yunusdanabas/evka_position/AGENT_LOG.md

# Agent Activity Log

Historical multi-agent collaboration log. Most recent first.
Format: `date | agent | summary`.

This file is preserved as a historical record; for working rules see
[AGENTS.md](AGENTS.md). Entries below were authored against the guidance files
that existed at the time (notably the git-ignored `CLAUDE.md` and the previous
in-repo `AGENTS.md`). Those historical mentions are intentionally left
unchanged.

## Activity Log

| Date | Agent | Changes |
|---|---|---|
| 2026-08-12 | Claude Code (Opus 5) | **Pre-handoff polish; the 2026-07-29 segfault WIP was wrong and is now actually fixed.** The committed `pytestmark = pytest.mark.forked` approach does not work: it **deadlocks the suite**, deterministically, on Python 3.10 in both a ROS-flavoured conda env and a clean CI-equivalent venv. `tools/calibration/tests/test_gui.py` sorts first and builds a `QApplication` in the parent, so `pytest-forked`'s `os.fork()` from a live-Qt parent inherits locks held by threads that don't exist in the child and blocks forever (killed at 300 s; once at 11 min). It went unnoticed because the recorded green run predates `pytest-forked` being installed — pytest silently ignores an unknown marker, so the markers were inert and the suite was running fully unforked. Replaced with the **two-invocation split** that `REMAINING_WORK.md` had predicted as the fallback: the six modules now carry `pytestmark = pytest.mark.qt_heavy` (registered in `pyproject.toml`), and CI runs `pytest -q -m qt_heavy --forked` then `pytest -q -m "not qt_heavy"` as separate steps — the forked parent never builds a QApplication, and the subtest-bearing modules stay unforked so failures can't be swallowed. Measured in a clean venv (Python 3.10.18, PyQt5 5.15.11, pyqtgraph 0.14.0, numpy 1.26.4, pytest-forked 1.7.5): 44 forked + 160 unforked & 11 subtests = 204; **12 consecutive runs of each pass, 0 failures / 0 segfaults / 0 hangs**; fault injection into a forked module returns `rc=1` and names the test. CI also now installs `pytest-forked` at all (it never did). **Other handoff fixes**: stale `191 tests / 45 checks` corrected to the measured 204/50 in `README.md`, `HANDOFF.md`, and `docs/integration/final_integration_validation.md`; `REMAINING_WORK.md`'s false "seven uncommitted files / last pushed `9553b35`" preamble rewritten (tree is clean, HEAD is current); `numpy` capped `<2` in `requirements.txt` **and** `pyproject.toml` with the Wine/`crealf` reason inline, since that constraint previously lived only in this log; STA defaults (`WIFI_STA_DEFAULT_SSID`/`_PASS` in `firmware/src/SphericalSensor.h`) disclosed in `HANDOFF.md`'s credential section — every doc described the AP credentials and none mentioned the STA ones, in a public repo; dead `.gitignore` rules removed (C# `bin/`/`obj/`/`*.dll`/`*.pdb`/`*.cache`, non-existent `tools/analysis/`, `tools/web_server/`) and `build/`/`dist/` anchored to `/build/`, `/dist/`; `tools/VISUALIZATION_GUIDE.md` deleted (gitignored so it could never clone, unreferenced, and described Three.js/Plotly work never done); v3 DRC JSON + `-backups` debris removed from the v4 PCB workspace and the v3 DRC JSON too, clearing the **last `/home/yunusdanabas` absolute paths from tracked files** (now 0); `matplotlib` requirement noted inline in `laser_radius/report/figures/make_figures.py`. Re-uploaded `EvkaGUI-src-v0.2.1.zip` to the v0.2.1 release so both assets now match local sha256 exactly (the published one had been stamped `02ff485`). Verified: compileall, IPT solver (0.405 mm), 204 pytest, 50 dashboard checks, all 10 PlatformIO envs, fresh-clone link check. No hardware, no flash, no KiCad edits, no history rewrite. |
| 2026-07-31 | Claude Code (Opus 5) | **v0.2.1 released with two GUI zips (one cross-built under Wine)**: tagged `v0.2.1` on `02ff485` and published the GitHub release with two assets. (1) `EvkaGUI-src-v0.2.1.zip` (~172 KB) — new `packaging/evka_gui/build_source_zip.sh`, portable Python source for Linux/macOS operators who previously had no packaged artifact at all; uses `git archive` so only tracked files at HEAD can enter a published zip, and smoke-tests by launching the GUI from a clean extraction. (2) `EvkaGUI-win64-v0.2.1.zip` (79.2 MB) — **cross-built on Linux under Wine 9.0**, not on Windows. Verified as far as that allows: `PE32+ x86-64` binary, `qwindows.dll` bundled, extracted zip ran 40 s in replay mode with no crash log (reference `build_windows.ps1` check is 8 s). **Not verified**: Wine emulates `qwindows.dll` rather than running it natively, and the serial/`COM3` path cannot be exercised under Wine — both stated in the release notes, which ask for a real-Windows check before distribution. **Wine gotcha recorded**: `winetricks vcrun2022` does NOT fix `ucrtbase.dll.crealf` (it installs `ucrtbase.dll` but no `api-ms-win-crt-*` forwarders, so Wine keeps its builtin); the working fix was pinning numpy 1.26.4, since numpy 2.x calls `crealf` on import — meaning this artifact diverges from a real Windows build, which would get numpy 2.x. Prefix lives at the gitignored `/.wine-build/`. Also documented both builders in `packaging/evka_gui/README.md` (`build_source_zip.sh` was previously undocumented) and anchored gitignore rules for both release zips. Found and corrected: the v0.2.0 release asset was stale (built from `04f26e4`, before the export work) — an earlier answer in this session said "no zip needs updating" after checking only the repo and missing GitHub Releases entirely. No hardware, no flash, no KiCad edits. |
| 2026-07-31 | Claude Code (Opus 5) | **Sensor readings in session exports + version 0.2.1**: saved-point and snapshot CSV exports now carry the streamed `wire_mm,theta_deg,phi_deg` triple, appended after the existing columns so position-indexed readers keep working; missing readings are blank cells (blank stays distinguishable from a real `0.0`). `x/y/z` are derived from the spherical triple and EMA-filtered in firmware, so position alone could not be traced back to what the encoders read. Desktop: latched in `_on_sensor` before any software-zero, row types widened in `tools/evka_gui/session_utils.py`, call sites in `tools/evka_gui/gui.py`; the REC session dump was left alone — it is already raw `DATA,` lines whose fields 4/5/6 are exactly this triple, and `parse_line` requires exactly 9 fields. Web dashboard: same columns in `firmware/src/WebDashboard.cpp` (`lastWtp`, cleared on `ws.onclose` so a stale reading cannot attach to a point saved after reconnect). **Latent bugs fixed in the same change**: `gui.py::_refresh_reference_overlays` unpacked saved-point rows as 4-tuples and raised `ValueError` on every 3D repaint once a point was saved (no test covered it; caught by an end-to-end run, regression test added); `tools/calibration/gui.py` shares `write_saved_points_csv` and would have broken on the widened rows, so it latches and exports the triple too. **Duplication removed**: `_export_session` and the dashboard's `endSession` each hand-rolled the CSV/download that `write_saved_points_csv` and `downloadCsv` already provide. Bumped host-tools version `0.2.0`→`0.2.1` in `pyproject.toml`, `build_windows.ps1`, and the tracked docs (historical `AGENT_LOG.md`/`REMAINING_WORK.md` mentions preserved). No Windows zip is checked in — `build_windows.ps1` builds one on Windows from the live `tools/` tree, so no packaging change was needed; validated the spec and import graph with `packaging/evka_gui/build_linux.sh` (frozen app launched and stayed up). Verified: 204 pytest, 50 dashboard checks, compileall, IPT solver (0.405 mm), all 10 PlatformIO envs, `git diff --check`. No hardware, no flash, no KiCad edits. |
| 2026-07-31 | Cursor Agent (Composer) | **README flash commands**: added PlatformIO upload/monitor examples for main device (`esp32s3_v4`, classic `wemos_d1_r32`) and remote control (`button_remote`, optional `button_remote_test`) to [README.md](README.md) and [README_TR.md](README_TR.md). Docs-only; no flash, hardware, or tests. |
| 2026-07-29 | Claude Code (Opus 5) | **Segfault isolation attempt (INCOMPLETE — uncommitted WIP in tree)**: pursued the open CI segfault. Established that blanket `pytest --forked` **fixes** it (0/20 segfaults on Python 3.10 vs 3/20 baseline, ~13 s/run) but is **unsafe**: fault injection proved it silently swallows failing `unittest` subtests — an injected bad assertion in `tools/position_checker/tests/test_math_conventions.py` reported `rc=0, 14 passed` under `--forked` while the same fault correctly reported `rc=1, 7 failed` without it. Blanket forking therefore rejected. Switched to **selective** isolation: added `pytestmark = pytest.mark.forked` to the six pyqtgraph-heavy modules (`test_calibration_report`, `test_command_tracking`, `test_disconnect`, `test_ipt_panel`, `test_recording`, `test_view3d`) so subtest-bearing modules keep normal reporting, plus `pytest-forked>=1.6` in `requirements.txt`. **This selective approach is NOT yet verified** — the 20-run measurement exceeded a 10-minute timeout (forking is much slower) and was stopped before a single clean run was timed. Changes are left uncommitted in the working tree. Remaining steps, evidence, and decision rationale recorded in [REMAINING_WORK.md](REMAINING_WORK.md). Also updated [docs/CI_PYTEST_SEGFAULT_LOG.md](docs/CI_PYTEST_SEGFAULT_LOG.md) with the `--forked` findings. Decisions confirmed by user this session: leave commit `711abf3`'s inaccurate "Playwright" body alone (documented, no history rewrite); god-file splits and missing-module tests approved but **not started**. No hardware, no flash, no KiCad edits, no push. |
| 2026-07-29 | Claude Code (Opus 5) | **Workspace health audit + fixes**: audited the 15-commit rewrite window (`0121b7f`..`33d837b`) — history scope/order/messages clean, no secrets or generated artifacts, `master` synced with `origin/master`. Fixed: `tools/webdash_harness/package.json` hardcoded `python` (failed rc=127 on any host without the alias; CI only passed because `setup-python` provides one) → `python3`; guarded the `PyQt5.QtWebSockets` import in `tools/evka_gui/ws_client.py` so the whole GUI package no longer fails to import on distro PyQt5 (Debian/Ubuntu ship QtWebSockets separately) with `WsClient()` raising a clear error instead, plus `tests/test_ws_import_guard.py`; added `compileall` and IPT-solver steps to `.github/workflows/ci.yml` (both were in AGENTS.md but not CI); removed trailing whitespace in `docs/ASYNCTCP_STACK_OVERFLOW_ANALYSIS.md`; deleted the empty stray `pcb_design/EVKA_position_v3/docs/`. **Found CI red on `master` and did NOT fix it**: `pytest` intermittently segfaults (exit 139) inside pyqtgraph's global `ViewBox.AllViews` walk when building a `PlotWidget` — measured 3/20 failures on Python 3.10, 0/20 on 3.12. Four candidate fixes were implemented, measured, and reverted as ineffective or harmful; full investigation, traceback, failure-rate table, and recommended next step (process isolation via `pytest-forked`) recorded in [docs/CI_PYTEST_SEGFAULT_LOG.md](docs/CI_PYTEST_SEGFAULT_LOG.md). Also noted: commit `711abf3`'s body says "Playwright" but the harness is jsdom (not amended — history already pushed); `v0.2.0-prototype` tag sits on `backup/pre-split-20260729`, not on `master`. Verified: 193 pytest, 45 dashboard checks, compileall, IPT solver (0.405 mm), and all 5 PlatformIO envs. No hardware, no flash, no KiCad edits, no history rewrite. |
| 2026-07-29 | OpenCode (GLM-5.2) | **Agent guidance consolidation (4 commits)**: (1) created tracked `AGENT_LOG.md` preserving the full historical activity table; (2) rewrote `AGENTS.md` as a concise universal agent guide and removed the `AGENTS.md`/`CLAUDE.md`/`CODEX.md`/`COPILOT.md` exclusions from `.gitignore` so guidance changes transfer on clone; (3) replaced retired `CLAUDE.md` and old activity-log references across `docs/ASYNCTCP_STACK_OVERFLOW_ANALYSIS.md`, `docs/resources.md`, `docs/hardware_design/12v_legacy/README.md`, `docs/hardware_design/12v_legacy/12v/circuit_schematic_12v.md`, `laser_radius/RESEARCH_PROMPT.md`, `laser_radius/kinematics_and_calibration.md`, `laser_radius/firmware_integration.md`; (4) indexed `AGENTS.md` and `AGENT_LOG.md` in `HANDOFF.md` and `docs/README.md`, and added this entry. Moved the local unpushed `v0.2.0-prototype` tag to the final commit. No pushes, tests, hardware checks, or remote changes. |
| 2026-07-29 | OpenCode (GPT-5.6) | **Agent guidance consolidation**: split the multi-purpose `AGENTS.md` into a concise tracked [AGENTS.md](AGENTS.md) working guide and this tracked `AGENT_LOG.md` history store; deleted the redundant git-ignored `CLAUDE.md`; removed the `AGENTS.md`/`CLAUDE.md`/`CODEX.md`/`COPILOT.md` exclusions from `.gitignore` so guidance changes cannot remain silently local; updated active `CLAUDE.md` and old activity-log references in `HANDOFF.md`, `docs/README.md`, `docs/resources.md`, `laser_radius/RESEARCH_PROMPT.md`, `laser_radius/kinematics_and_calibration.md`, `laser_radius/firmware_integration.md`, `docs/ASYNCTCP_STACK_OVERFLOW_ANALYSIS.md`, `docs/hardware_design/12v_legacy/README.md`, and `docs/hardware_design/12v_legacy/12v/circuit_schematic_12v.md`; preserved historical mentions inside this log. Moved the local unpushed `v0.2.0-prototype` tag to the final commit. No pushes, tests, hardware checks, or remote changes. |
| 2026-07-29 | OpenCode (GPT-5.6) | **Prototype handoff implementation and software freeze**: completed unified GUI/dashboard/calibration correctness work; added strict response tracking, STATUS parsing, timeout recovery, zero-relative RAW diagnostics, ACK-confirmed PPR flows, report overlap/stale-artifact guards, transactional session writes, and candidate-transform safety. Removed vendor C# sources, rejected shared calibration JSON, evka_gui_v2 shims, and tracked LaTeX intermediates. Set host tools 0.2.0 / Python 3.10+, pinned the jsdom dashboard harness, expanded CI, finalized self-contained English/Turkish handoff/protocol/calibration docs, and retained hardware validation as explicitly deferred. Software-only verification: 191 pytest, 45 dashboard checks, compileall, IPT solver (0.405 mm), and all 10 PlatformIO environments passed; no flash, hardware check, push, or remote change. |
| 2026-07-29 | OpenCode (GPT-5.6) | **Post-cleanup documentation reconciliation**: updated active handoff, onboarding, protocol, calibration, integration, v4, and host-tool docs for completed vendor C# deletion, host tools `0.2.0` / Python 3.10+, pending software-verification result slots, and no checked-in shared/default calibration JSON. Canonical `tools/evka_gui` remains sensor-frame-only; a passing session JSON is documented only as an explicit `--legacy-visualizer --calibration PATH` input. Preserved archived C# history as clearly deleted. Docs-only; no builds, tests, uploads, or hardware checks. Verified `git diff --check` and 130 active relative Markdown links across 29 files. |
| 2026-07-29 | OpenCode (GPT-5.6) | **Approved prototype firmware/dashboard correctness**: retained zero-relative `RAW_COUNTS`; centralized one-response command dispatch so serial/TCP/WebSocket errors are consistent; made `CAL_W` use count magnitude with strict finite/range validation; made classic/v4 encoder signs board-specific without changing pins; added WPA2 63-character password limit and verified NVS ACKs; made dashboard rotary PPR sharing explicit and apply/save status ACK+CONSTANTS-driven; rejected overlong/full WebSocket commands instead of truncating/dropping silently. Verified embedded JS syntax plus `pio run -e wemos_d1_r32` and `pio run -e esp32s3_v4`. |
| 2026-07-16 | OpenCode (GPT-5.5) | **Calibration report CLI**: added `python -m tools.calibration.report` default workflow. First run creates `docs/calibration/sessions/current/calibration_points.csv` and `validation_points.csv`; subsequent runs generate `report.md`, `calibration.json`, `calibration_errors.csv`, and `validation_errors.csv` from the filled CSVs using the existing Kabsch solver. Added focused tests under `tools/calibration/tests/` and documented the command in `tools/calibration/README.md`. |
| 2026-07-14 | OpenCode (GPT-5.5) | **ButtonRemoteTest pin-scan command + flash**: added TCP/USB serial commands to `firmware/tests/ButtonRemoteTest/ButtonRemoteTest.cpp` (`PING`, `PINS`, `HELP`), with `PINS` reporting GPIO `0,1,2,3,4,5,6,7,8,9,10,20,21` while excluding flash pins `11–17` and USB `18/19`. Added **READ PINS** button/display to `tools/remote_tester/remote_test_gui.py`. Built and flashed `button_remote_test` to `/dev/ttyACM0`; serial sanity check returned `PINS,GPIO0=1,...,GPIO21=1` and AP `REMOTE_TEST` came up at `192.168.4.1`. Verify: `pio run -e button_remote_test`; `pio run -e button_remote_test --target upload --upload-port /dev/ttyACM0`; USB serial `PINS`; `python -m compileall tools/remote_tester tools/evka_gui -q`. |
| 2026-07-14 | OpenCode (GPT-5.5) | **evka_gui no-dock/no-scroll layout pass**: moved protocol log from bottom dock into a compact left-column panel, removed the left `QScrollArea`, moved IPT / Points / Diagnostics into tabs, moved Battery and ESP-NOW remote into Diagnostics, and moved right-column controls above the plot grid so the bottom/right area remains plots. Compact connection panel now permits 50/50 split at 1366×768 and 1920×1080. Verify: `pytest tools/evka_gui/tests -q` 34 passed; `python -m compileall tools/evka_gui -q`; offscreen 1920×1080 split `[957, 957]`, 1366×768 split `[680, 680]`; no `QDockWidget`, left panel is `QWidget`. |
| 2026-07-14 | OpenCode (GPT-5.5) | **evka_gui full-page polish + bug pass**: restored true 50/50 maximized splitter behavior with horizontally expanding control panel, enlarged/stretch-based saved-points list, compact 160px protocol-log dock, and 2D origin/saved-point layer markers. Fixed protocol log UI-thread updates, TCP XYZ log classification, WebSocket connect timeout/state cleanup, malformed `POINT` parsing, rejected IPT solution action gating, and Remote Tester TCP thread cleanup. Added focused tests for protocol classification, WebSocket URL parsing, control-line ingestion, saved-points CSV, and profiles. Docs updated for inline Quick IPT + WebSocket examples. Verify: `pytest tools/evka_gui/tests -q` 34 passed; `python -m compileall tools/evka_gui -q`; offscreen `EvkaWindow`/`RemoteTesterWindow` smoke OK; offscreen 1920×1080 split `[957, 957]`, 1366×768 split `[680, 680]`. |
| 2026-07-14 | Cursor Agent | **evka_gui layout de-clutter**: left control column capped at 540px with view-first splitter (480/1120 default, stretch 0:1); Commands / Points / Diagnostics moved into tab widget (SYSINFO + PPR + raw counts in Diagnostics); quick commands in 3-column grid; saved-points list max height 140px; view grid row/column stretch for larger 3D/2D plots; Quick IPT spacing tightened (`ipt_panel.py`). Protocol log dock + replay bar (replay-only) unchanged. Tests: 27 passed; offscreen `EvkaWindow` OK. |
| 2026-07-14 | Cursor Agent | **Remote tester layout fix**: `_header_widget()` hook in `remote_test_gui.py` with log stretch; `remote_window.py` dev note via hook instead of `insertWidget(0)` (was clipping fixed 580px layout); min 480×560, default 520×680. |
| 2026-07-14 | Cursor Agent | **EVKA GUI full enhancement (Phases 1–6)** — session: snapshot capture/clear/export CSV (`session_utils.py`), saved-points CSV export, saved-point label refresh on SW zero (`UserRole` + `_refresh_saved_point_labels`), connection profiles (save/load/delete via `QSettings`). UI polish: plot layer toggles (trail/IPT/origin/saved), trail max spinbox, keyboard shortcuts (`Z`/`S`/`A`/`Esc`), copy axis/Rθφ buttons, threshold alerts (invalid position, low battery, low heap). Transport/diagnostics: WebSocket mode (`ws_client.py`, QWebSocket port 80 `/ws`, `--ws HOST` CLI), protocol log dock (`protocol_log.py`), Open Dashboard toolbar, CONSTANTS/PPR strip, `RAW_COUNTS` firmware command → `RAW,<θ>,<φ>,<wire>` in `EvkaPosition.cpp` + `model.py` parsing. IPT depth: Copy P / export capture CSV / Add P to snapshots in `ipt_panel.py`, 3D IPT overlay on `_View3D` (`position_checker/gui.py`), sweep hints from `solver.py` constants. Replay: pause/speed/step/slider seek with replay-from-zero rebuild (`replay_utils.py`). Calibration: Kabsch write `calibration.json` + endpoint CSV import in `calibration.py`. Remote: **Remote Tester…** secondary window (`remote_window.py`, wraps `tools/remote_tester`). Key files: `gui.py`, `session_utils.py`, `protocol_log.py`, `ws_client.py`, `replay_utils.py`, `remote_window.py`, `ipt_panel.py`, `wifi_window.py`, `ipt_window.py`, tests `test_session_utils.py`, `test_replay_utils.py`, `test_ipt_panel.py`, `test_ipt_window.py`, `test_model.py`. Docs: `tools/evka_gui/README.md`, `docs/gui_unification/LOG.md`, `PLAN.md`, `CMD_SOFTWARE_INTEGRATION.md`, `README.md` (RAW_COUNTS), `remote_tester/README.md`. Verify: `pytest tools/evka_gui/tests -q` 27 passed, `pio run -e esp32s3_v4` OK, offscreen `EvkaWindow` OK. Deferred: laser radius GUI (no firmware); live `calibration.json` transform in GUI. |
| 2026-07-14 | Cursor Agent | **Inline IPT + WiFi window** (plan: inline IPT on main page): created `tools/evka_gui/ipt_panel.py` — inline **Quick IPT** group (L, ARM/STOP/SOLVE/CLEAR, P/L_hat/RMS/cond/status) on main scroll panel; green cloud + orange target + dashed sphere overlays on session XY/XZ/YZ plots via `_refresh_ipt_overlays()` in `gui.py`; always feed raw lines in `_drain` (sensor frame, not SW-zero offsets). Created `tools/evka_gui/wifi_window.py` — **WiFi Settings…** secondary window (SSID/password, Save & Reboot, Forget, router IP); removed WiFi credential fields from main panel. Compact SYSINFO one-liner strip (RSSI · heap · uptime · TCP). Refactored `ipt_window.py` → `IptPlotsWindow` (plots-only pop-out sharing `IptPanel` state); toolbar **IPT plots…**. Tests: `test_ipt_panel.py`. Doc sweep: `docs/gui_unification/PLAN.md`, `tools/evka_gui/README.md`, `tools/README.md`, `CMD_SOFTWARE_INTEGRATION.md`, `HANDOFF.md`, `CONTRIBUTING.md`. |
| 2026-07-14 | Cursor Agent | **Quick IPT in evka_gui**: toolbar **Quick IPT…** secondary window (`tools/evka_gui/ipt_window.py`) fed from main `_drain` with raw protocol lines; reuses `tools/ipt` capture/solver; standalone `python -m tools.ipt` unchanged. Tests: `tools/evka_gui/tests/test_ipt_window.py`. Doc sweep: README, tools/README, HANDOFF, CONTRIBUTING, PLAN, CMD integration, v4 FIRMWARE, ipt README. |
| 2026-07-13 | OpenCode (GPT-5.5) | **Python EVKA GUI 3D view rotation**: changed only the unified Python GUI initial 3D camera by parameterizing `_View3D` defaults and instantiating `tools.evka_gui` with `rot_x=30.0`; left coordinate math, data signs, browser dashboard, and legacy standalone visualizer default unchanged. |
| 2026-07-13 | OpenCode (GPT-5.5) | **v4 encoder sign correction**: flipped `ENCODER_THETA_SIGN` to `+1.0f` and `ENCODER_PHI_SIGN` to `-1.0f` after field check showed upward motion produced negative phi/Z and desired +Y produced negative theta/Y. Updated `CLAUDE.md`, `docs/ARCHITECTURE.md`, and `docs/calibration/README.md`; no pin-map changes. Verified `pio run -e esp32s3_v4`. |
| 2026-07-13 | OpenCode (GPT-5.5) | **v4 THETA/WIRE port swap**: backed up `pcb_design/EVKA_position_v4/` to `/tmp/opencode/EVKA_position_v4_backup_20260713_141439/`; updated v4 KiCad schematic, PCB, and BOM CSV so J1 is WIRE and J3 is THETA while leaving PHI on J2; updated `SphericalSensor.h` v4 pins to THETA GPIO9/10 and WIRE GPIO7/8; updated current v4 docs/calibration notes with connector order and encoder cable color codes; copied missing TP4056, MT3608, and ESP32-S3 symbol/footprint assets into the repo-local v4 `libs/` and added project `sym-lib-table`. |
| 2026-07-09 | OpenCode (Qwen) | **Bosch PLR 40 C integration research — RESOLVED** (docs-only, no firmware/PCB changes): Bluetooth type discrepancy resolved — Bosch's official PLR 30 C / PLR 40 C manual explicitly states **"Bluetooth 4.2 (Low Energy)"** and **"must support the GATT profile."** ESP32-S3 compatibility confirmed (BLE-only chip matches BLE-only device). Protocol decrypted from GLM family: BLE UUIDs (`02a6c0d0-...` service, `02a6c0d1-...` characteristic), CRC-8 (polynomial 0xA6, init 0xAA), IEEE 754 float parsing (bytes 7-10, little-endian), command table (continuous sync `C0 55 02 01 00 1A`, single measure `C0 40 00 EE`). **However:** byte-level traces are from GLM 50C/50CG/120C — not yet verified on physical PLR 40 C. One real-device capture session required before firmware work. USB interface: none (no USB port on PLR 40 C). **Recommendation updated:** do not use PLR 40 C for production — BLE latency jitter, no wired fallback, 5-minute auto-power-off, power supply fragility make it unsuitable for continuous automated tracking. Use wired industrial sensors (Meskernel LDK-40/LDL-T or Dimetix D-Series) instead. Updated `laser_radius/bosch_plr_40c_integration.md` with full confirmed details, NimBLE code sketches, risk assessment. Updated `laser_radius/version_a_handheld_devices.md` §2.3 to mark Bluetooth type as confirmed. Updated `laser_radius/firmware_integration.md` §2 with confirmed BLE details, UUIDs, CRC-8 code, IEEE 754 parsing. Updated `laser_radius/README.md` executive summary and folder index. Deleted `laser_radius/BOSCH_PLR_40C_DEEP_RESEARCH_PROMPT.md` (research complete). |
| 2026-07-09 | OpenCode (Qwen) | **Bosch PLR 40 C integration research** (docs-only, no firmware/PCB changes): discovered critical Bluetooth type discrepancy — prior docs stated "BLE 4.2 only (GATT)" but the only community reference implementation ([philipptrenz/BOSCH-GLM-rangefinder](https://github.com/philipptrenz/BOSCH-GLM-rangefinder), archived 2024-07-03) uses **classic Bluetooth RFCOMM (SPP)**, not BLE. Created `laser_radius/bosch_plr_40c_integration.md` with full analysis: reverse-engineered protocol details (measure command `\xC0\x40\x00\xEE`, response parsing `uint32(data[2:6]) * 0.05` mm), ESP32-S3 integration sketches for both SPP and BLE paths, verification steps (nRF Connect scan to determine Bluetooth type), and risk assessment. Created `laser_radius/BOSCH_PLR_40C_DEEP_RESEARCH_PROMPT.md` with comprehensive research prompt for further investigation (Bluetooth type verification, protocol confirmation, USB interface investigation, ESP32-S3 specific integration, comparison with alternatives). Updated `laser_radius/version_a_handheld_devices.md` §2.3 to flag both measurement principle AND Bluetooth type as unconfirmed (two independent flags). Updated `laser_radius/firmware_integration.md` to add §2 (Bosch PLR 40 C protocol details) and corrected interface table to note Bluetooth type is unconfirmed. Updated `laser_radius/README.md` folder index with new files. |
| 2026-07-09 | OpenCode (GPT-5.5) | **GUI consolidation and battery protocol parity**: created the tracked unification plan/log under `docs/gui_unification/`, established `tools/evka_gui` as the canonical Python operator GUI with `python -m tools.evka_gui` / `evka-gui`, added deprecated `tools/evka_gui_v2` compatibility shims, and updated docs to point users at the unified GUI. Added missing operator features in the canonical GUI (TCP/WebSocket connect paths, replay-safe controls, min/max/origin-distance display/export, per-axis zero, calibration capture helpers) while leaving `tools/ipt/` and `tools/remote_tester/` untouched. Added TCP/WebSocket `BATT,<voltage>,<pct>,<is_low>` parity after `STATUS`, WebDashboard battery polling/display, and Windows CMD `BATT` parsing. Verified `pytest tools/evka_gui/tests -q`, `python -m compileall tools/evka_gui tools/evka_gui_v2 tools/position_checker`, offscreen Qt `EvkaWindow` instantiate, `pytest -q` (62 passed), `pio run -e esp32s3_v4`, and `dotnet build CMDScanner.csproj` (success with existing nullability warnings). |
| 2026-07-01 | Claude Code | **Laser radius study — extended hardware research + report restore** (docs-only, no firmware/PCB changes): restored the accuracy-vs-range chart (Figure 1) to `laser_radius/report/report.tex` after it was removed in a prior pass. Ran two parallel Copilot CLI research agents (per user request) to broaden the device shortlist: Version A gained 8 candidates (Hilti PD-I, Leica DISTO D2/S910, Bosch GLM 50-27CG/165-27CG, Stanley TLM165i, RS PRO/CEM iLDM-150H — cheapest BLE handheld found at ~$90-130 — and ADA Cosmo 60 Green), plus 5 more rejected devices documented (DeWalt DW099S too-short-range, Makita LD050P no interface, Skil ME981901, Trimble/Spectra Precision QM-series no interface, Nikon Forestry Pro II wrong tech). Version B gained 5 industrial candidates (Micro-Epsilon optoNCDT ILR1181-3/ILR2250/ILR3800, WayCon LDI, Jenoptik LDM4x, Scantron SLS) plus a documented 13-manufacturer rejection list (SICK/Banner/Wenglor/Balluff/Contrinex/Riftek/di-soric/Acuity/Pepperl+Fuchs/Baumer confirmed wrong tech; ifm O1D inconclusive; Jenoptik LDM7x/LDM301-302 same-family-different-tech trap) and one flagged near-miss (Leuze ODSL 30 — genuinely phase-based but %-accuracy, fails spec anyway). Total qualifying shortlist grew from 5 to 17 devices. Updated all 5 `laser_radius/*.md` files + `README.md` with the expanded tables and standout picks (Leica DISTO S910 = best overall spec with native USB; RS PRO ILDM-150H = potential Bosch price replacement). Regenerated `report/figures/accuracy_vs_range.png` with 5 representative lines (two "meets spec" flat-accuracy bands, JRT's slight-growth line, and two "fails spec" examples for different reasons — wrong tech vs. right-tech-wrong-accuracy-type). Added a curated "Extended Shortlist" table + updated recommendations to `report/report.tex`, fixed a table-column overflow, recompiled clean (6 pages). |
| 2026-07-01 | Claude Code | **Laser radius study re-scoped to a fixed spec + LaTeX report** (docs-only, no firmware/PCB changes; supersedes the tiered version below from earlier the same day): user fixed the actual requirement — range ≤40 m, laser device accuracy ≤10 mm (device spec, not combined-system XYZ, confirmed with user) — replacing the earlier 3-tier framework. Rewrote all 5 `laser_radius/*.md` files + `README.md`: the physics dividing line is phase-shift (AMCW) vs. pulsed-ToF measurement — the entire Benewake TF-series (previously the Version B primary pick) fails the new spec (±5cm–±1%, 5–40× over budget) and is now excluded with the physics reason documented; new shortlist is JRT B605B (≈±2.6mm@40m, RS232 TTL, primary low-cost pick, works as Version A or B), Meskernel LDL-T (±1mm/80m, 30Hz), Bosch PLR 40C (±2mm confirmed flat across full 0.05–40m range, BLE fallback, best Turkey stock), Leica DISTO X4/D-series (±1mm, premium, genuine RS232 accessory cable), Dimetix D-series (±1mm, RS232/RS422, confirmed CHF 1,769–2,437 on manufacturer's own shop — primary Version B industrial pick). Noted the Version A/B convergence at this accuracy bar (bare OEM modules work either mounted style). `kinematics_and_calibration.md` §4 reframed the combined-error-budget finding (encoders alone contribute ≈17.8mm at 40m regardless of laser choice) as informational context, not a redesign trigger, per the user's explicit scope decision. Added **`laser_radius/report/`**: a 6-page LaTeX report (`report.tex`/`report.pdf`, compiles clean with `pdflatex`) summarizing the study, with 2 generated matplotlib figures (`figures/accuracy_vs_range.png`, `figures/error_budget.png`), a TikZ kinematic-chain diagram, and TikZ placeholder boxes (not `\includegraphics`) for hardware photos the user will add later under `report/images/`. |
| 2026-07-01 | Claude Code | **Laser radius detailed study** (docs-only, no firmware/PCB changes) — superseded same day by the entry above: expanded the brief into 5 new files under `laser_radius/` — `version_a_handheld_devices.md` (5 wired-serial/BLE candidates incl. JRT B605B, Meskernel LDL, Dimetix DLS-B, Bosch PLR 40 C BLE fallback; explains why UNI-T LM50A has no automated data path), `version_b_integrated_modules.md` (TF02-i-RS485 primary + 5 alternatives, Modbus wiring), `kinematics_and_calibration.md` (laser offset geometry, `CAL_R`/`ZERO_R` workflow proposal replacing `CAL_W`, combined error-budget table showing encoder angular error dominates at 40m regardless of laser choice), `firmware_integration.md` (interface options, 20Hz feasibility, BLE+WiFi coexistence notes, `LaserRadiusSensor` API sketch — design only, not implemented), `procurement_and_bom.md` (pricing/suppliers, bench-test order). Key finding: the brief's RS-485 GPIO 13/14/18 baseline came from the archived `12v_legacy/v2` pin plan; the current as-built 5V v2 board wires those pins differently (13/14=AUX header, 18=BTN2) — documented corrected wiring (13/14/15) as an open item for PCB-owner review, no `.kicad_sch` touched. Updated `laser_radius/README.md` with an executive summary, 3 proposed requirement tiers, and an A-vs-B recommendation; updated folder index. Research sourced via live web search (device specs/pricing/Turkey availability), with unverified figures explicitly flagged "verify before order" throughout. |
| 2026-07-01 | Cursor Agent | **Laser radius research at repo root**: Moved brief to `laser_radius/README.md`; added `laser_radius/RESEARCH_PROMPT.md` for Claude deep-dive; left redirect stub at `docs/research/laser_radius_research.md`. Detailed files (Version A/B, kinematics, firmware, BOM) to be added under `laser_radius/`. |
| 2026-07-01 | Cursor Agent | **Laser radius research brief**: Added `docs/research/laser_radius_research.md` — preliminary doc for spherical variant with 2 rotary encoders + laser (not draw-wire). Covers Version A (detachable handheld; wired serial preferred, Bosch PLR BLE fallback; LM50A noted unsuitable) and Version B (built-in Benewake TF02-i-RS485). ESP32-S3 phi-head mounting, kinematic chain, pin baseline, open questions for full research phase. Docs-only; no firmware changes. |
| 2026-06-24 | Cursor Agent | **Encoder sign constants for +Z up / +X forward**: Added `ENCODER_THETA_SIGN` (-1.0) and `ENCODER_PHI_SIGN` (+1.0) in `SphericalSensor.h`; applied in `countsToSpherical()` (replaces hardcoded phi negation). Updated `CLAUDE.md`, `AGENTS.md`, `system_architecture.md`, `docs/calibration/README.md`. Verified `pio run -e wemos_d1_r32` + pytest (42 tests). |
| 2026-06-24 | Cursor Agent | **CMD GUI Software Zero fix + audit**: Added `tools/position_checker/cmd_display.py` with testable offset/refresh logic. Fixed immediate R/θ/φ refresh on Software Zero click; added Clear Software Zero button, SW ZERO badge, invalid-position XYZ styling, SYSINFO TCP count, open-network WiFi, disconnect state reset, saved-point display/world labels + ERR:NO_POINTS dialog, legacy BAGLI_DEGIL STA_IP. Updated `cmd_gui.py`, `parser.py` (isfinite on XYZ/SENSOR), C# `gui.cs` parity (immediate refresh + ACK-wait WiFi). Added `test_cmd_gui_zero.py`, `test_tcp_client.py`. Updated `tools/README.md` and `docs/integration/CMD_SOFTWARE_INTEGRATION.md`. 42 tests pass. |
| 2026-06-24 | OpenCode (Qwen) | **IPT feature implementation**: Created `tools/ipt/` package with Quick IPT hidden-point measurement (sphere-fit solver, armed capture buffer, PyQt5 GUI). Added finite-value guard to TCP ingest, clarified known-L semantics (L_fit for sanity check), expanded README with workflow/troubleshooting/limitations. Created LaTeX technical report under `docs/reports/ipt/`. Added IPT to `tools/README.md` and root `README.md`. Fixed network doc inconsistencies: aligned `README.md`, `CLAUDE.md`, and `docs/integration/CMD_SOFTWARE_INTEGRATION.md` with firmware source of truth (`SphericalSensor.h`: STA IP `192.168.1.84`, GW `192.168.1.254`, SSID `ASMETAL`). All 39 tests pass. |
| 2026-04-29 | OpenCode (kimi-k2.6) | **Archived all 12V hardware designs** into `docs/hardware_design/12v_legacy/` after project direction changed away from 12V. Moved folders: `12v`, `12v_tht`, `v2`, `v3`, `final_design`, `comparison`. Updated all internal and external cross-references in `AGENTS.md`, `CLAUDE.md`, `firmware/src/SphericalSensor.h`, and files inside `12v_legacy` (including KiCad schematic text fields and presentation HTML). Added `12v_legacy/README.md` as archive index. |
| 2026-04-29 | OpenCode (GPT-5.5) | Expanded onboard-charging comparison guidance in `docs/hardware_design/12v_legacy/comparison/`: added V3-D charger module choices (12.6V 1A/2A/4A, Type-C 2A, IP2369/IP2326 PD branches), BMS pairing table (6A/20A/25A/40A/60A plus Daly/JBD preference), charge-only vs power-path/load-sharing architecture ranking, and Options A/B/C for future onboard charging. Updated the 18-slide comparison deck and `final_design/README.md` future-revision guidance while keeping Final Design as external-balance-charge-only. |
| 2026-04-29 | OpenCode (GPT-5.5) | Reworked `docs/hardware_design/12v_legacy/comparison/` deliverables in English: rewrote `HARDWARE_COMPARISON.md` as the primary Final Design decision guide, rebuilt `presentation/index.html` as an 18-slide Reveal.js companion, and updated `README.md` to recommend Final Design consistently. Corrected TP5100 3S charging claims based on source review plus external fact check, clarified Schottky OR priority ambiguity, added 1S/2S/3S LiPo charging-method comparisons, added optional `V3-D Onboard 3S Charger Module` branch with verified charger+BMS/load-isolation requirements, updated `final_design/README.md` future onboard-charging guidance, and downgraded Final Design wording from validated to reviewed/selected pending ESP32-S3 firmware migration and physical validation. |
| 2026-04-27 | OpenCode (GPT-5.5) | Created `docs/hardware_design/12v_legacy/final_design/` as the final recommended build package copied from the V3-A direction and extended into a single 12V-only external-charge design. Added README, source-copy manifest, final schematic, BOM, LPKF layout guide, pin assignment, external charging procedure, validation checklist, and `firmware/pin_assignment_final.h`. Final design adds `D_ADAPT` adapter isolation to prevent battery backfeed into the adapter-sense/Q_BATT gate rail and omits onboard charging/V3-B/V3-C options. |
| 2026-04-27 | OpenCode (GPT-5.5) | Created `docs/hardware_design/12v_legacy/comparison/README.md`, an independent comparison of the legacy 5V board, original 12V design, 12V all-THT variant, V2 industrial ESP32-S3 design, and V3-A/B/C simple ESP32-S3 variants. Covered individual pros/cons, safety, manufacturing, firmware readiness, use-case fit, and final recommendation of V3-A for new core 12V builds. |
| 2026-04-27 | Claude Code | **V3 hardware documentation review** (code-review pass, docs-only fixes). Found 3 issues: (F1) ADC tap inconsistency — block diagram showed `V12_PROT`, section 6 said `BUCK_VIN`; fixed block diagram in `circuit_schematic_v3.md` and removed hedge in `pin_assignment_v3.md` line 12. (F2) `BMS_3S` qty was `0-1 optional`; changed to `1 required` with protection note in `bill_of_materials_v3.md`. (F3) Missing V3 navigation link from `docs/hardware_design/12v_legacy/12v_tht/README.md`; added. Confirmed correct: IRF4905 pinout, GPIO 1 ADC safety, encoder pin assignments, LC filter values (22µH+220µF), 1nF C_SIG warning, blade fuse mandatory, external charging policy, 12v→V3 and v2→V3 cross-links. Open gates: power-path module selection TBD; ESP32-S3 platformio.ini environment not yet added (deferred). |
| 2026-04-27 | OpenCode (GPT-5.5) | Created **V3 simple 12V hardware documentation package** under `docs/hardware_design/12v_legacy/v3/`: ESP32-S3-DevKitC-1 core-only carrier, internal 3S LiPo RC backup with external balance charging, generic ready-made power-path module interface, IRF4905 input RPP, MP1584EN/equivalent buck, retained proven 7-channel encoder dividers/ferrites/TVS, removed V2 default RS-485/I2C/watchdog/spare headers/onboard charging. Added README, schematic, BOM, LPKF layout guide, pin assignment, power-path module interface, external charging procedure, validation checklist, and `firmware/pin_assignment_v3.h`; linked V3 from 12V/V2 docs and CLAUDE.md. |
| 2026-04-23 | OpenCode (Kimi k2.6) | **V2 Hardware Redesign — complete design document package** under `docs/hardware_design/12v_legacy/v2/`: ESP32-S3-DevKitC-1 migration with full GPIO remap (Theta→4/5, Phi→6/7, Wire→15/16/17, ADC→1), CN3767 switch-mode charger (replaces TP5100+MT3608, -44% heat), MP2315 buck (lower ripple), IRF4905 TO-220 RPP, MAX485 RS-485/Modbus RTU onboard, MAX813L external watchdog, I2C expansion header (DS3231/ADS1115), 4 spare GPIOs, 4 status LEDs, DIN rail mounting, LPKF S63 compatible 100% THT layout. Created: `README.md`, `circuit_schematic_v2.md`, `bill_of_materials_v2.md`, `pcb_layout_guide_v2.md`, `pin_assignment_v2.md`, `remote_pendant_v2.md`, 4 subsystem docs, and `firmware/pin_assignment_v2.h`. Old V1 designs preserved. |
| 2026-04-13 | Codex (GPT-5.3) | Visual Studio flashing triage hardening: updated `docs/integration/setup_test_guide.md` with explicit "PlatformIO-only" guidance for vendors using classic Visual Studio, added root-folder requirements (`platformio.ini` + `firmware/`), added canonical `pio run`/`upload`/`monitor` sequence and explicit `--upload-port` fallback, documented `/dev/ttyS0` auto-detect failure mode, and added a failure artifact checklist for escalations. Validation run: `pio run -e wemos_d1_r32` ✅, `pio run -e wemos_d1_r32 --target upload` failed as expected on host without USB device (`Could not open /dev/ttyS0`). |
| 2026-04-13 | Claude Code | DWEM2 migration: replaced all active-doc `DWE3000` references with `DWEM2`; reset `PPR_WIRE` from 8020 (DWE3000-calibrated) to 8000 (DWEM2 P2000 theoretical) in test files (`DrawWireTest.cpp`, `AllSensorsTest.cpp`) and docs; updated `CLAUDE.md`, `AGENTS.md` config table, `individual_hardware_test_plan.md`, `setup_test_guide.md`, `PCB_HAND_SOLDERING_AND_DEBUG.md`, `PCB_EMI_LAYOUT_GUIDE.md`, `12v/circuit_schematic_12v.md`, `improvement_research.md`, `ESP32_NVS_CALIBRATION_GUIDE.md`, `ESP32_PCNT_REFERENCE.md`, `docs/calibration/README.md`. Current draw corrected from ~100 mA to ~25 mA (datasheet: <40 mA @ 24 V). Historical files kept unchanged. |
| 2026-04-10 | Codex (GPT-5.3) | Adjusted STA static networking to match observed CMD_FUAR subnet from live host diagnostics (`ip a` showed `192.168.0.167/24`): updated `SphericalSensor.h` static STA IP/GW to `192.168.0.84` / `192.168.0.1`, updated Python CMD GUI default target in `tools/position_checker/cmd_main.py`, updated local `settings.txt` target IP, and synced `README.md` + `CLAUDE.md` static profile docs accordingly |
| 2026-04-10 | Codex (GPT-5.3) | Implemented STA static IP profile for router mode while preserving AP fallback: added `WIFI_STA_STATIC_IP_*`, `WIFI_STA_GW_*`, `WIFI_STA_SN_*`, `WIFI_STA_DNS_*` constants in `firmware/src/SphericalSensor.h`; applied `WiFi.config(...)` before each `WiFi.begin(...)` in `firmware/src/WebDashboard.cpp` reconnect path; updated `README.md` and `CLAUDE.md` to document fixed STA profile (`10.0.0.84/24`, GW `10.0.0.1`, DNS `8.8.8.8`) with AP unchanged at `192.168.1.50`; verified by `pio run -e wemos_d1_r32` |
| 2026-04-10 | Claude Code | Multi-agent audit (Explore ×3, Gemini, Copilot) of all 2-week agent changes. Firmware fixes: (1) `CalibrationTest.cpp` Theta/Phi pins swapped → corrected to THETA=14/12 PHI=32/35. (2) `SphericalSensor.cpp` NVS PPR load: added `isfinite` + range check [100, 500000] to catch negative/corrupt values. (3) `EvkaPosition.cpp`: removed dead `recording_active` + `RECORD_TOGGLE` command, `uint16_t pt_idx` → `uint32_t`, eliminated duplicate NVS read via `WebDashboard::isStaConfigured()`. (4) `WebDashboard.cpp`: added `ERR:` handler in JS `onWsMessage`, fixed false "will reboot" status text, extended `.invalid` CSS to all 3 XYZ cards, fixed watchdog addition overflow (both `_staConnectAttemptMs` and `_staLostIpMs` watchdogs now use safe `(int32_t)(now-ts) >= (int32_t)timeout` form). (5) `WebDashboard.h`: added `isStaConfigured()` accessor. Repo cleanup: collapsed 6 redundant ESPAsync/WebSocket docs into `docs/ESPASYNCHACK_NOTES.md`, deleted `docs/microros/` (feature never built), deleted `docs/EXTENSIVE_AUDIT_2026-04-08.md` (superseded), fixed broken `.gitignore` patterns for `docs/firmware/` subdirectory. Dependencies: added `numpy`, `PyQt5`, `pyqtgraph` to `pyproject.toml` + CI. Build: `pio run -e wemos_d1_r32` ✅ (898 473 B). Tests: `pytest -q` 29 passed ✅ |
| 2026-04-10 | Codex (GPT-5) | Completed second documentation/cross-reference sweep: fixed remaining broken relative links in `docs/hardware_design/assembly/individual_hardware_test_plan.md`, aligned reference docs (`docs/firmware/ESP32_PCNT_REFERENCE.md`, `docs/firmware/FreeRTOS_Dual_Core_Architecture.md`, `docs/microros/MICROROS_ESP32_INTEGRATION.md`, `docs/hardware_design/encoders/draw_wire/README.md`) to the current Theta 14/12 and Phi 32/35 mapping, and rechecked internal markdown references |
| 2026-04-10 | Codex (GPT-5) | Reconciled current-use docs to `firmware/src/SphericalSensor.h` as the source of truth (Theta 14/12, Phi 32/35, Wire 16/17), removed a duplicate `WEBSOCKET_CLIENT_DISCONNECTION_CLEANUP.md` activity-log row, added minimal GitHub Actions CI for `pytest -q` + `pio run -e wemos_d1_r32`, and verified repo references against the April 9 WiFi/ESPAsync doc bundle |
| 2026-04-09 | Codex (GPT-5.3) | Implemented WiFi reconnect hardening for associated/no-IP stalls in `firmware/src/WebDashboard.cpp` / `firmware/src/WebDashboard.h`: added `STA_LOST_IP_RECOVERY_MS` watchdog state (`_staLostIpMs`) so prolonged `STA_LOST_IP` triggers controlled reconnect without breaking W7 slow-DHCP protection or W8 capped backoff behavior; updated `docs/WIFI_PERFORMANCE_ISSUES_LOG.md`; verified with `pio run -e wemos_d1_r32` + `pytest -q` |
| 2026-04-09 | Codex (GPT-5) | Fixed two follow-up WiFi recovery findings in `firmware/src/WebDashboard.cpp` / `firmware/src/WebDashboard.h`: added separate STA association tracking so the watchdog no longer restarts valid DHCP-pending joins, saturated the disconnect counter to preserve capped backoff during long outages, updated `docs/WIFI_PERFORMANCE_ISSUES_LOG.md`, and verified with `pio run -e wemos_d1_r32` + `pytest -q` |
| 2026-04-09 | Codex (GPT-5.3) | Reconciled WiFi/ESPAsync docs and cross-references with current firmware behavior: updated reliability wording in `README.md` / `README_TR.md`, fixed `setAutoReconnect` guidance in `docs/WIFI_PERFORMANCE_ISSUES_LOG.md`, and replaced stale contradictory deep-dives with aligned versions of `docs/ESPASYNCHACK_ISSUES_CROSS_REFERENCE.md`, `docs/ESPASYNCHACK_MEMORY_LEAK_GUIDE.md`, `docs/ESPASYNCHACK_QUICK_REFERENCE.md`, `docs/MILLIS_OVERFLOW_ANALYSIS.md`, `docs/WEBSOCKET_CLIENT_DISCONNECTION_CLEANUP.md`, and `docs/WEBSOCKET_HEAP_FRAGMENTATION_WORKAROUNDS.md`; also updated `docs/ASYNCTCP_STACK_OVERFLOW_ANALYSIS.md` cleanup terminology |
| 2026-04-09 | Codex (GPT-5) | Fixed two WiFi recovery review findings in `firmware/src/WebDashboard.cpp`: STA disconnects now trigger AP health verification without forced SoftAP/DHCP restart when AP is already healthy, and the initial STA connection no longer double-calls `WiFi.begin()` on boot; synced `docs/WIFI_PERFORMANCE_ISSUES_LOG.md` and verified with `pio run -e wemos_d1_r32` + `pytest -q` |
| 2026-04-09 | Claude (Copilot CLI) | Created `docs/ESPASYNCHACK_ISSUES_CROSS_REFERENCE.md`: navigation index mapping all 8 ESPAsyncWebServer v1.x issues to their corresponding deep-dive documentation (6 main guides, 7 total), mitigation status, issue selection guide ("What problem am I experiencing?"), integration with project, and when-to-use guide for each document |
| 2026-04-09 | Claude (Copilot CLI) | Created `docs/WEBSOCKET_CLIENT_DISCONNECTION_CLEANUP.md`: deep-dive on WebSocket client disconnection flow, TCP RST handling, zombie client detection/accumulation, and slot cleanup mechanics; documented Issue #2 (memory not reclaimed on disconnect), TCP RST bypass scenarios, and all cleanup patterns used in this project (on-connect, on-disconnect, periodic fallback, low-heap emergency); includes root-cause analysis, recommended practices, and comprehensive testing checklist |
| 2026-04-09 | Claude (Copilot CLI) | Created `docs/ESP32_WDT_20HZ_QUICK_REFERENCE.md`: WDT timeout troubleshooting for 20 Hz loop + WiFi active; explains default 5 sec watchdog timeout, root causes (blocking I/O, stack overflow, STA reconnect stalls), 20 Hz timing analysis (all operations <8 ms, ~6 loops per position update), red-flag symptoms, 5-step diagnosis checklist, common pitfalls with fixes, production readiness checklist, and cross-references to async/memory/WiFi docs |
| 2026-04-09 | Claude (Copilot CLI) | Created `docs/ESP32_WIFI_AP_STA_HEAP_DRAIN_GUIDE.md`: comprehensive guide on IDF 4.4.x DHCP lease memory leak in AP+STA concurrent mode (5–50 KB loss per client cycle, 100–200 B/min idle drift, OOM after 24–72 hours); explains root causes (DHCP server/client cache not reclaimed on disconnect, ARP/DNS caches retained indefinitely), provides diagnostics (heap logs, fragmentation detection, event monitoring), documents 4 mitigation strategies (periodic soft reset, aggressive DHCP cleanup, client churn limiting, IDF 5.x upgrade), includes Tier 1/2/3 implementation plan with configuration constants for EVKA firmware |
| 2026-04-09 | Claude (Copilot CLI) | Created `docs/WEBSOCKET_HEAP_FRAGMENTATION_WORKAROUNDS.md`: deep operational guide for 24+ hour uptime with 20 Hz WebSocket broadcasts (5 KB/min baseline drift), explaining per-client allocation chain, fragmentation mechanism over time, 5 practical workarounds (split payloads, aggressive cleanup triggers, queue depth monitoring, compaction, pre-allocation pools), monitoring/diagnostics patterns, 24-hour stress test protocol, production deployment checklist, and operational optimization guidance for heap drift >3 KB/min |
| 2026-04-09 | Claude (Copilot CLI) | Created `docs/ESPASYNCHACK_QUICK_REFERENCE.md`: symptoms→issue troubleshooting card with common mistakes (don't forget cleanup, don't broadcast >2KB, don't block callbacks), deployment checklist (20 Hz rate ✅, cleanup ✅, validation ✅, heap monitor ✅, WiFi resilience ✅), and stress-test guidance |
| 2026-04-10 | Claude (Sonnet 4.6) | Enabled `ENABLE_REMOTE_WIFI_CONFIG=1` and fixed two bugs: (1) `WIFI_SET` handler called `ESP.restart()` before returning, so `dashboard.broadcast()` and `cmdTcp.sendToAllClients()` in `loop()` were never reached — added explicit broadcasts before `delay(500)+restart`; (2) `forgetWifi()` JS showed premature "cleared" status before firmware response — changed to neutral "Sending forget request...". Updated compile-time STA defaults to `CMD-YAZILIM`. Updated `CLAUDE.md`, `README.md`, `docs/integration/CMD_SOFTWARE_INTEGRATION.md`, `docs/WIFI_PERFORMANCE_ISSUES_LOG.md` to reflect new flag state and STA network. Feature verified working: `WIFI_SET` saves to NVS and reboots device, `ACK:WIFI_SAVED` now reaches TCP/WS clients before restart. |
| 2026-04-09 | Claude (Copilot CLI) | Created `docs/ASYNCTCP_STACK_OVERFLOW_ANALYSIS.md`: comprehensive technical analysis of ESP32 task stack overflow risks in AsyncTCP + WebSocket + WiFi AP+STA mode; documents default lwIP task stack (4096 words / 16 KB), root causes, observable symptoms, mitigation strategies (6 total: 5 implemented, 1 optional); includes test scenarios, heap/stack monitoring guidance, and production recommendations |
| 2026-04-09 | Claude (Copilot CLI) | Created `docs/ESPASYNCHACK_MEMORY_LEAK_GUIDE.md`: comprehensive guide on ESPAsyncWebServer v1.x known issues (8 issues documented: 6 HIGH/MEDIUM severity, Issue #8 FIXED), root-cause analysis of `textAll()` per-client allocation leak, memory not reclaimed on disconnect, fragmented RX buffers, WiFi STA orphan state, event loop re-entrancy, slow-client queue bloat, IDF 4.4+ cleanup race; includes production stability checklist and current project mitigation status (✅ 20 Hz rate limit, periodic cleanup, input validation, WiFi resilience, heap monitoring) |
| 2026-04-09 | Claude (Copilot CLI) | Created `docs/WIFI_AP_STA_RECONNECT_PATTERNS.md`: comprehensive guide on WiFi.begin() safety in AP+STA mode, explaining how AP+STA coexistence works, documenting that WiFi.begin() does NOT disrupt AP clients, detailing all 8 known issues (1-7 fixed, 8 mitigated), providing best-practice reconnect patterns, configuration constants, and operational checklist. Referenced from `docs/WIFI_PERFORMANCE_ISSUES_LOG.md` |
| 2026-04-09 | Codex (GPT-5.3) | Final docs/cross-reference sync after AP resilience patch: updated `README.md`, `README_TR.md`, and `docs/integration/CMD_SOFTWARE_INTEGRATION.md` with STA-disconnect AP recovery behavior and links to `docs/WIFI_PERFORMANCE_ISSUES_LOG.md` |
| 2026-04-09 | Codex (GPT-5.3) | Hardened AP availability after STA loss: added WiFi STA connect/disconnect event handling, AP health reassertion + controlled STA reconnect backoff in `WebDashboard`, wired non-blocking `dashboard.tick()` in main loop, verified with `pio run -e wemos_d1_r32`, and documented as Issue 8 in `docs/WIFI_PERFORMANCE_ISSUES_LOG.md` |
| 2026-04-08 | Cursor Agent | `docs/BLE_WIFI_COEXISTENCE.md` Section 4 example: BLE latency storage/sum/avg use `uint32_t`/`uint64_t` to avoid >65.5 ms sample wrap and sum/avg overflow; added `stdint.h` for `UINT32_MAX` |
| 2026-04-08 | Codex (GPT-5.3) | Implemented audit remediations: unified WiFi command gating across serial/TCP/WebSocket (`ENABLE_REMOTE_WIFI_CONFIG` + `ERR:WIFI_CFG_DISABLED`), made `STATUS` return network-visible response, replaced WebSocket pending `String` handoff with a lock-protected queue, tightened dashboard dirty redraw triggers, aligned sensor validity/filter behavior (validate on published clamped spherical + reset EMA priming on invalid/zero), hardened Python TCP timeouts/keepalive, synchronized STA defaults/docs, fixed integration/doc cross-links, standardized E40S6 naming, and pinned PlatformIO platform/lib versions |
| 2026-04-05 | Codex | 12V PCB pack in `docs/hardware_design/12v_legacy/12v/` (spec, schematic, BOM, layout, KiCad in `12v/kicad/`); firmware `BATTERY_ADC_12V_INPUT` + ADC scaling in `SphericalSensor.h`; `CLAUDE.md` / `AGENTS.md` paths updated |
| 2026-04-04 | Codex (GPT-5.3) | Reduced serial invalid-position spam in `firmware/src/SphericalSensor.cpp` by adding small limit tolerances for startup jitter and throttling `! INVALID POSITION` logs to 1 Hz while continuing to emit DATA frames for tooling |
| 2026-04-04 | Codex (GPT-5.3) | Centralized visualizer protocol/pin conventions in `tools/position_checker/cmd_main.py`, refactored Python visualizer parsing to consume shared constants, fixed negative-phi drift by preserving firmware spherical fields after XYZ transform, aligned Windows CMD GUI parsing constants/helpers, and added tests/docs for consistency |
| 2026-04-04 | Codex (GPT-5.3) | Fixed startup invalid-position spam by allowing zero-home radius (`RADIUS_MIN_MM` 50→0 in `firmware/src/SphericalSensor.h`), and synced `CLAUDE.md` configuration table |
| 2026-04-03 | Codex (GPT-5.3) | Added root README documentation for building the legacy Windows CMD GUI executable with `dotnet publish` and included the expected `CMDScanner.exe` output path |
| 2026-04-03 | Codex (GPT-5.3) | Added STA-IP auto-sync behavior in both CMD GUIs: when `STA_IP:<ipv4>` is received, client connect target IP is auto-updated (Windows `firmware/src/CMD Soft/gui.cs`, Linux `tools/position_checker/cmd_gui.py`), retained AP fallback behavior, and updated `tools/README.md` to current defaults (`192.168.1.84` STA example, `192.168.1.50` AP fallback, `WIFI_SET`, `settings.txt`) |
| 2026-04-03 | Codex (GPT-5.3) | Added STA-IP usage documentation with confirmed ASMETAL example (`STA_IP:192.168.1.84`) in `README.md` and `docs/CMD_SOFTWARE_INTEGRATION.md`, and changed CMD GUI default TCP target IP to `192.168.1.84` in both Linux (`tools/position_checker/cmd_gui.py`) and Windows (`firmware/src/CMD Soft/gui.cs`) clients while preserving AP fallback documentation (`192.168.1.50`) |
| 2026-04-03 | Codex (GPT-5.3) | Fixed cross-repo consistency and hardening issues: aligned wiring docs/tests to `SphericalSensor.h` (Theta 14/12, Phi 32/35, Wire 16/17), corrected spherical formula docs to firmware convention, added `ENABLE_REMOTE_WIFI_CONFIG` default OFF to block TCP WiFi credential writes unless explicitly enabled, synchronized Python dependencies in `pyproject.toml`, and added minimal CI workflow for Python tests + PlatformIO build |
| 2026-04-03 | Codex (GPT-5.3) | Verified `settings.txt` handling: confirmed it was not ignored, added ignore rules (`settings.txt`, `**/settings.txt`) to prevent accidental commits of WiFi/network credentials, and validated no existing git history for the file |
| 2026-03-30 | Codex (GPT-5) | Verified tracked .NET build outputs under `firmware/src/CMD Soft/bin` and `obj`, added `.gitignore` rules for C# artifacts (`bin/`, `obj/`, `*.dll`, `*.pdb`, `*.deps.json`, etc.), and removed those generated files from git tracking with `git rm --cached` |
| 2026-03-30 | Codex (GPT-5) | Updated legacy Windows CMD GUI (`firmware/src/CMD Soft/gui.cs`) for current TCP responses, added standalone WinForms project files (`CMDScanner.csproj`, `Program.cs`), and documented single-file self-contained EXE publish command/output |
| 2026-03-30 | Codex (GPT-5) | Replaced legacy `INTEGRATION_GUIDE.md` with `docs/CMD_SOFTWARE_INTEGRATION.md`, updated README/CLAUDE/tools/CMD Soft docs to current CMD WiFi+TCP defaults, and refreshed doc cross-references |
| 2026-03-27 | Codex (GPT-5) | Added Linux TCP CMD panel under `tools/position_checker` (`tcp_client.py`, `cmd_gui.py`, `cmd_main.py`) with ESP32 command compatibility (`GET_IP`, `ZERO`, `WIFI_AYAR`), plus tools README run/protocol docs |
| 2026-03-17 | Claude Code | Production polish: pin swap (Theta→32/35, Phi→14/12), wire sign negation, 20Hz DATA output, pyqtgraph GL viz upgrade, WiFi AP + web dashboard (ENABLE_WIFI), Copilot artifact cleanup, doc sync |
| 2026-03-03 | Codex (GPT-5) | Resolved code-review findings: restored valid data flow after zeroing by validating limited spherical state, hardened replay loader against missing/unreadable files, and added replay loader unit tests |
| 2026-03-03 | Codex (GPT-5) | Added hardware calibration files pack under `docs/calibration/` (theta/phi/draw-wire procedures, CSV templates, final calibration record template) and linked Phase 7 roadmap + final integration validation checklist |
| 2026-03-03 | Codex (GPT-5) | Implemented Phase 5-7 software completion: firmware non-blocking serial commands (`ZERO`,`PING`,`STATUS`), battery monitor compile flag default OFF, validity-flow fix, visualizer reconnect/replay/csv logging/performance upgrade, unit tests, integration validation doc, and diagram-tool path wrappers |
| 2026-03-11 | Claude Code | Phase 5: PPR_ROTARY corrected 1480→20000 (X4 quadrature confirmed), PPR_WIRE calibrated 2000→8020 (400 mm/1604 mm), interactive CalibrationTest.cpp + DrawWireTest CAL_W added, all docs updated |
| 2026-02-26 | Claude Code | Phase 4: Updated PPR_ROTARY 5000→1480, synced all docs, cleaned repo, created AGENTS.md and PROJECT_ROADMAP.md |
| 2026-02-21 | Claude Code | Phase 3: Remapped phi pins GPIO 3→27, GPIO 5→26 |
| 2026-02-18 | Claude Code | Phase 2: DWE3000 quadrature rework, pin remap 6/7→16/17 |
