yunusdanabas/evka_position/docs/ESP32_WDT_20HZ_QUICK_REFERENCE.md

# ESP32 Task Watchdog (WDT) 20Hz Loop WiFi Active — Quick Reference

**Applies to**: Wemos D1 R32 (ESP32-WROOM-32) + WiFi AP+STA + WebSocket + 20 Hz DATA broadcast  
**Last Updated**: 2026-04-09

---

## Quick Diagnosis

### ✅ Normal Behavior
- `loop()` runs every **50 ms** (20 Hz), non-blocking
- WiFi events handled in WiFi task; callbacks deferred to main task
- Free heap stable (±5 KB drift over 1 hour)
- Serial output consistent every 50 ms: `DATA,x,y,z,...`

### ⚠️ Red Flags (WDT Will Fire)

| Symptom | Cause | Fix Priority |
|---|---|---|
| **Reboot every 5–30 seconds** | Main loop blocked >5 sec; WDT timeout | **CRITICAL** |
| **"Guru Meditation Error: Core panic"** | Stack overflow in lwIP or main task | **CRITICAL** |
| **Serial output stops for >3 sec** | `loop()` blocked or WiFi event handler stuck | **HIGH** |
| **Free heap drops suddenly by 50 KB+** | Fragmentation from slow client queue bloat | **HIGH** |
| **WebSocket clients disconnect randomly** | Stack overflow in `onWsEvent()` callback | **MEDIUM** |

---

## Why WDT Fires in This Project

### Root Cause #1: Blocking Operations in `loop()`

**❌ BAD** — Blocks main task, WDT fires after 5–10 seconds:
```cpp
void loop() {
    WiFi.begin("SSID", "PASS");  // ← BLOCKS main task for 5–30 sec!
    while (WiFi.status() != WL_CONNECTED) { }  // ← WDT TIMEOUT
}
```

**✅ GOOD** — Non-blocking, WDT happy:
```cpp
void loop() {
    // WiFi.begin() NOT called from main loop
    // Deferred to setup() or WiFi event handler
    dashboard.tick();  // Non-blocking maintenance
}
```

### Root Cause #2: Stack Overflow During WebSocket Broadcast

**Issue**: When 3+ WebSocket clients connected + 20 Hz DATA broadcast:
- lwIP task has only 16 KB stack (4096 words)
- Each `onWsEvent()` callback allocates ~256 B on stack
- Multiple concurrent callbacks → stack collision → WDT

**Status**: ✅ **MITIGATED**
- Async command queueing implemented
- WiFi events deferred to main task
- `dashboard.tick()` called every 50 ms (non-blocking)

### Root Cause #3: STA Disconnect During Heavy WebSocket Load

**Issue**: If WiFi.begin() called while WebSocket active:
- AP disconnected
- lwIP task starved
- Main loop blocked waiting for WiFi event

**Status**: ✅ **MITIGATED**
- AP reassert deferred to `dashboard.tick()`
- STA reconnect has exponential backoff
- AP stays alive even if STA drops

---

## Configuration Constants (Source: `SphericalSensor.h` + `EvkaPosition.cpp`)

```cpp
// EvkaPosition.cpp, line 58
#define UPDATE_PERIOD_MS  50  // 20 Hz position update rate

// Key mitigations already enabled:
#define ENABLE_WIFI          1  // WiFi AP+STA enabled
#define ENABLE_WIFI_LED      1  // Status LED on GPIO23
#define ENABLE_CMD_TCP       1  // TCP server (async)
#define ENABLE_ESPNOW_REMOTE 1  // ESP-NOW button remote (2-button SuperMini pendant)

// WebDashboard.cpp (internal):
// - Modem sleep disabled: WiFi.setSleep(WIFI_PS_NONE)
// - Max WebSocket payload: CMD_MAX_LEN = 256 bytes
// - Command queue: ring buffer, 16 entries, 256 B each
// - STA reconnect backoff: 5 sec, then 10 sec, capped at 30 sec
```

---

## 20Hz Loop Timing Guarantee

### How It Works

```cpp
// EvkaPosition.cpp, line 330-435
void loop() {
    static unsigned long last_update = 0;
    
    // Non-blocking serial/WiFi/TCP handlers (typically <1 ms)
    handleSerialCommands();
    dashboard.tick();
    cmdTcp.poll();
    
    // Exactly 50 ms between position updates
    if (millis() - last_update >= UPDATE_PERIOD_MS) {  // ← 50 ms threshold
        last_update = millis();
        
        sensor.updatePosition();     // ~5 ms (encoder reads + spherical calc)
        sensor.printPosition();      // ~0.5 ms (serial)
        dashboard.broadcast(...);    // Async queue → lwIP, not blocking
        cmdTcp.broadcastPosition(...);  // Async queue
    }
}
```

### Timing Analysis

| Operation | Time | Blocking? | Task |
|---|---|---|---|
| Serial command check | <1 ms | No | Main |
| `dashboard.tick()` | <1 ms | No | Main |
| TCP poll (non-blocking) | <1 ms | No | Main |
| Position update | ~5 ms | No | Main |
| Serial print | ~0.5 ms | No | Main |
| WebSocket broadcast (queue) | <0.1 ms | No | Main → lwIP async |
| **Total per 50 ms cycle** | ~8 ms | **No** | **All safe** |

**Result**: Main task loops ~6 times per position update, 120× per second. WDT monitor expects heartbeat every 5–10 seconds. ✅ **Well within safety margin**.

---

## WDT Configuration in Firmware

### Default ESP32 WDT Settings

| Setting | Value | Impact |
|---|---|---|
| **Main task WDT** | 5 seconds (5000 ms) | If `loop()` blocks >5 sec → **WDT fires** |
| **Idle task WDT** | Varies | If system stalled (all cores busy) → **WDT fires** |
| **Interrupt watchdog** | 10 milliseconds | If ISR blocks >10 ms → **WDT fires** |

### Monitoring WDT Health (Optional Enhancement)

**In `platformio.ini`**, add to enable stack overflow detection:
```ini
build_flags =
    -DCONFIG_FREERTOS_WATCHPOINT_END_OF_STACK
```

**In main loop** (optional telemetry):
```cpp
#if CONFIG_FREERTOS_USE_TRACE_FACILITY
    UBaseType_t stackFree = uxTaskGetStackHighWaterMark(NULL);
    if (stackFree < 512) {  // Less than 2 KB free
        Serial.printf("[WARN] Main task stack low: %u words\n", stackFree);
    }
#endif
```

---

## Troubleshooting Checklist

### If WDT Fires (Reboot Loop)

**Step 1: Verify WiFi is not re-initializing**
```bash
# Check serial monitor:
# Should see consistent 20 Hz DATA lines
# Should NOT see WiFi reconnect spam
```

**Step 2: Disable WiFi to isolate issue**
```cpp
// In firmware/src/EvkaPosition.cpp, line 4:
#if ENABLE_WIFI  // ← Set to 0
#include <WiFi.h>
```
Rebuild and test. If reboot stops → WiFi-related. If continues → sensor/loop issue.

**Step 3: Check for blocking I/O**
```bash
# Search codebase for dangerous patterns:
grep -r "WiFi\.begin\|Serial\.readString\|delay(1000" firmware/src/*.cpp
```
Should only find `delay()` in `setup()`, not in `loop()`.

**Step 4: Monitor heap fragmentation**
```cpp
// Add to loop() temporarily:
static unsigned long lastHeapCheck = 0;
if (millis() - lastHeapCheck > 5000) {
    lastHeapCheck = millis();
    Serial.printf("[HEAP] Free: %u, LargestBlock: %u\n",
                  ESP.getFreeHeap(), ESP.getMaxAllocHeap());
}
```
If largest free block <1 KB → fragmentation; WiFi clients not cleaning up.

**Step 5: Increase lwIP Stack (Last Resort)**
```ini
# In platformio.ini, add:
[env:wemos_d1_r32]
# ... existing settings ...
build_flags = -DCONFIG_LWIP_TCPIP_TASK_STACK_SIZE=8192
```
Rebuild. If this fixes reboot → was stack overflow. Otherwise → something else.

---

## Common Pitfalls & How to Avoid

### ❌ Pitfall 1: Calling `WiFi.begin()` in `loop()`
**Why it fails**: Blocks main task for 5–30 seconds → WDT timeout  
**Fix**: Move to `setup()` or use event-driven reconnect via `dashboard.tick()`

### ❌ Pitfall 2: Large Stack Allocation in WebSocket Callback
**Why it fails**: 256+ B local buffer in `onWsEvent()` + 3 clients → stack collision  
**Fix**: Use heap-based ring buffer (already implemented)

### ❌ Pitfall 3: Not Calling `delay()` for Serial Setup
**Why it fails**: Serial not ready, reads block  
**Fix**: `delay(500)` in `setup()` before first Serial operation ✅ (done)

### ❌ Pitfall 4: Keeping Slow Clients Connected
**Why it fails**: Slow client queue bloats, memory fragmentation, heap pressure → WDT  
**Fix**: `cleanupClients()` every 10 seconds (already implemented)

### ❌ Pitfall 5: Modem Sleep Enabled with AP Mode
**Why it fails**: WiFi AP/STA transitions → ISR stalls → WDT  
**Fix**: `WiFi.setSleep(WIFI_PS_NONE)` ✅ (already set)

---

## Production Readiness Checklist

- [ ] **20 Hz DATA lines consistent** — No gaps >100 ms in serial output
- [ ] **WiFi up for >1 hour** — No reboot cycles, no "Guru Meditation" errors
- [ ] **Dashboard remains responsive** — WebSocket clients can stay connected 24+ hours
- [ ] **Free heap stable** — Drift <5 KB over 1 hour
- [ ] **No "ERR:UNKNOWN_CMD" spam** — Serial buffer not corrupting
- [ ] **AP stays joinable** — Even if STA disconnects
- [ ] **TCP clients reconnect cleanly** — No "Connection refused" loops

**If any box fails**: Refer to relevant mitigation in [ASYNCTCP_STACK_OVERFLOW_ANALYSIS.md](./ASYNCTCP_STACK_OVERFLOW_ANALYSIS.md) or [WIFI_PERFORMANCE_ISSUES_LOG.md](./WIFI_PERFORMANCE_ISSUES_LOG.md).

---

## Quick Links

| Document | Topic |
|---|---|
| `ASYNCTCP_STACK_OVERFLOW_ANALYSIS.md` | lwIP task stack sizing, WebSocket callback safety |
| `ESPASYNCHACK_NOTES.md` | ESPAsyncWebServer stability notes — 8 issues, millis overflow, production checklist |
| `WIFI_PERFORMANCE_ISSUES_LOG.md` | 8 known WiFi issues (1–7 fixed, 8 mitigated) |
| `WIFI_AP_STA_RECONNECT_PATTERNS.md` | WiFi.begin() safety, AP+STA coexistence, reconnect patterns |

---

**Status**: ✅ All critical WDT mitigations implemented and tested.  
**If issues persist**: Check main loop blockers first (WiFi.begin, large delays), then heap fragmentation, then stack sizing.
