yunusdanabas/evka_position/docs/firmware/QUICK_REFERENCE_DualCore.md

# Quick Reference: ESP32 Dual-Core Implementation

## TL;DR

**Current:** 50 Hz polling → 50 ms latency
**Proposed:** 1 kHz encoder task (Core 0) + 20 Hz computation (Core 1) → 1 ms latency (50× faster)

---

## Maximum Safe Encoder Frequencies

| Method | Max Frequency | Your PPR_ROTARY (20k) | Safe RPM |
|---|---|---|---|
| **Software ISR** | 50–100 kHz | ~333 kHz @ 100k RPM | ✓ 1,000 (safe) |
| **PCNT Hardware** | 40 MHz | Safe to 333 kHz @ 100k RPM | ✓ 100,000 (safe) |

**Rule:** Stay <10 kHz for software ISR reliability. Use PCNT for >10 kHz.

---

## Core Allocation

```
Core 0 (Realtime)                Core 1 (General)
├─ encoderTask (Pri 3, 1 kHz)    ├─ computationTask (Pri 2, 20 Hz)
│  ├─ Read 3 encoders            │  ├─ Spherical/Cartesian transform
│  ├─ Send to queue              │  └─ Validate limits
│  └─ ~500 µs/cycle              │
└─ 50% CPU used                  ├─ serialTask (Pri 1, 10 ms)
                                 │  ├─ Print position
                                 │  └─ Read commands
                                 └─ ~1% CPU used
```

---

## xTaskCreatePinnedToCore Pattern

```cpp
xTaskCreatePinnedToCore(
    taskFunction,       // Function pointer
    "TaskName",         // Debug name
    2048,              // Stack size (bytes)
    nullptr,           // Parameters
    3,                 // Priority (3=high, 1=low)
    nullptr,           // Handle (optional)
    0                  // Core ID (0 or 1)
);
```

---

## Queue Operations

| Operation | Usage |
|---|---|
| `xQueueCreate(depth, itemSize)` | Create queue |
| `xQueueOverwrite(handle, item)` | Send (replaces old, never blocks) |
| `xQueueReceive(handle, item, timeout)` | Read (blocks if empty) |
| `xQueuePeek(handle, item, timeout)` | Read without removing |

---

## Data Structures

```cpp
struct EncoderCounts {  // 16 bytes (encoder → computation)
    int32_t theta_counts;
    int32_t phi_counts;
    int32_t radius_counts;
    uint32_t timestamp_ms;
};

// SystemStatus already defined (computation → serial)
```

---

## Queue Configuration

**Encoder Queue:** 20 items × 16 bytes = 320 bytes
- Send: `xQueueOverwrite()` (never blocks Core 0)
- Receive: `xQueueReceive()` with 50 ms timeout
- Strategy: Drop old counts (only latest matters)

**Position Queue:** 10 items × 64 bytes = 640 bytes
- Send: `xQueueOverwrite()` (for display)
- Receive: `xQueueReceive()` with 10 ms timeout

---

## Core 0 Task (1 kHz Encoder Polling)

```cpp
void encoderTask_core0(void *pvParameters) {
    TickType_t xLastWakeTime = xTaskGetTickCount();
    const TickType_t xFrequency = pdMS_TO_TICKS(1);  // 1 ms = 1 kHz
    
    EncoderCounts counts;
    int32_t prev_theta = 0, prev_phi = 0, prev_radius = 0;
    
    while (1) {
        // Read encoders (~450 µs)
        counts.theta_counts = thetaEncoder->read();
        counts.phi_counts = phiEncoder->read();
        counts.radius_counts = wireEncoder->read();
        counts.timestamp_ms = millis();
        
        // Rate limit: only send if changed
        if (counts.theta_counts != prev_theta ||
            counts.phi_counts != prev_phi ||
            counts.radius_counts != prev_radius) {
            
            xQueueOverwrite(encoderQueue, &counts);
            prev_theta = counts.theta_counts;
            prev_phi = counts.phi_counts;
            prev_radius = counts.radius_counts;
        }
        
        // Maintain 1 kHz cycle
        vTaskDelayUntil(&xLastWakeTime, xFrequency);
    }
}
```

---

## Core 1 Task (20 Hz Computation)

```cpp
void computationTask_core1(void *pvParameters) {
    TickType_t xLastWakeTime = xTaskGetTickCount();
    const TickType_t xFrequency = pdMS_TO_TICKS(50);  // 50 ms = 20 Hz
    
    EncoderCounts counts;
    SystemStatus status;
    
    while (1) {
        // Wait for encoder data (up to 50 ms)
        if (xQueueReceive(encoderQueue, &counts, pdMS_TO_TICKS(50)) == pdTRUE) {
            
            // Apply offsets and transform
            int32_t theta = counts.theta_counts - THETA_OFFSET;
            int32_t phi = counts.phi_counts - PHI_OFFSET;
            int32_t radius = -(counts.radius_counts - RADIUS_OFFSET);
            
            SphericalCoords sph = sensor.countsToSpherical(theta, phi, radius);
            CartesianCoords cart = sensor.sphericalToCartesian(sph);
            uint8_t is_valid = validateLimits(sph, cart);
            
            // Prepare status
            status.position = cart;
            status.spherical = sph;
            status.is_valid = is_valid;
            status.frame_count++;
            status.last_update_ms = counts.timestamp_ms;
            
            // Send to serial task
            xQueueOverwrite(positionQueue, &status);
        }
        
        vTaskDelayUntil(&xLastWakeTime, xFrequency);
    }
}
```

---
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
