yunusdanabas/evka_position/docs/firmware/firmware_rework_log.md

# Firmware Rework Log — Draw-Wire Encoder (DWE3000 Quadrature)
_Session: 2026-02-18_

> **Note (2026-03-09):** File paths in this log reflect the pre-reorganization layout.
> Current paths: `firmware/src/` (production), `firmware/tests/` (test sketches).

---

## Summary

The original firmware treated the draw-wire encoder as a single-channel clock + direction pin.
The OPKON DWE3000 is a full quadrature encoder (A, B, Z channels).
GPIO 6/7 were also on the flash-reserved range of ESP32-WROOM-32.
This rework corrects both issues.

---

## Files Changed

### 1. `firmware/DrawWireTest/DrawWireTest.cpp` — Full rewrite

**Before:** ISR on clock pin (GPIO 6), direction read from GPIO 7, PPR=1000, MM_PER_PULSE=1.0

**After:** Encoder library on GPIO 16/17 (quadrature A/B), Z-index ISR on GPIO 18,
PPR=2000, MM_PER_PULSE=0.1

Key changes:
- `#include <Encoder.h>` added
- Heap-allocated `Encoder* wireEnc = new Encoder(PIN_WIRE_A, PIN_WIRE_B)` replaces ISR
- `PIN_WIRE_CLK 6` / `PIN_WIRE_DIR 7` → `PIN_WIRE_A 16` / `PIN_WIRE_B 17`
- `PPR_WIRE 1000` → `2000`
- `MM_PER_PULSE = 1000.0/1000.0 = 1.0` → `DRUM_CIRCUM_MM/PPR_WIRE = 200.0/2000.0 = 0.1`
- Z index channel added: `volatile uint32_t z_count = 0; void IRAM_ATTR zISR()`
- Serial output now: `COUNT=<n>  DIST_mm=<n*0.1>  Z_ticks=<z_count>`

---

### 2. `firmware/EvkaPosition/SphericalSensor.h` — Three edits
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
