yunusdanabas/evka_position/docs/hardware_design/assembly/REVERSE_POLARITY_PROTECTION.md

# P-MOSFET Reverse Polarity Protection Circuit (12V)
## AO3401A Design Guide

---

## Overview

The **AO3401A** is a P-channel MOSFET ideal for reverse polarity protection in 12V automotive/battery applications. This circuit blocks current flow when the input polarity is reversed, preventing damage to downstream components.

**Key Parameters:**
- Gate-Source threshold voltage: Vgs(th) = -0.5V (typ.)
- Drain current (continuous): Id = 4.2A @ Vgs = -10V
- On-resistance: Rds(on) = 0.14Ω (typ.) @ Vgs = -4.5V
- Drain-Source voltage: Vds(max) = 20V
- Body diode: Integrated (forward voltage ~0.7V at 2A)

---

## Schematic: Standard Reverse Polarity Protection

```
    +12V_IN
       |
      [M1]
      /    AO3401A P-channel MOSFET
    G/     Gate connected to chassis ground
   /____   Source (arrow) connects to +12V_OUT
       |
      [Load]
       |
      GND
```

### Circuit Description

1. **Input Polarity (Correct)**
   - **+12V** connects to **Drain (D)**
   - **GND** connects to **Source (S)** and **Gate (G)**
   - Gate-Source voltage: Vgs = -12V (negative, P-channel ON)
   - Mosfet conducts → Current flows through Drain-Source
   - Load receives full 12V

2. **Input Polarity (Reversed)**
   - **GND** connects to **Drain**
   - **+12V** connects to **Source**
   - Gate-Source voltage: Vgs = 0V (threshold not reached, P-channel OFF)
   - Mosfet is reverse-biased → No current flows
   - Load is protected (no voltage applied)

---

## Detailed Schematic with Gate Resistor

```
    +12V_IN
       |
       +------+
              |
            [R1]  Gate pull-down resistor
              |   (10kΩ - 100kΩ)
              |
      +-------+------- Gate (G)
      |
     [M1]    AO3401A
    D |  S
      |  |
    [D1] +------- +12V_OUT
      |  |        (to Load)
      |  |
     GND GND
```

### Component Values

| Component | Value | Purpose |
|---|---|---|
| **M1** | AO3401A | P-channel MOSFET |
| **R1** | 10kΩ - 100kΩ | Gate pull-down resistor (10kΩ typical) |
| **D1** (Optional) | 1N4148 or Schottky | Optional: Parallel to ensure low reverse voltage drop |

### Resistor Selection Rationale

**Gate Resistor (R1):**

| Value | Use Case |
|---|---|
| **10kΩ** | Standard for low EMI, moderate switching noise (preferred) |
| **100kΩ** | Higher impedance, very low leakage if gate floating |
| **1kΩ** | Lower impedance; use only if strong gate drive needed (rare) |

**Recommended: 10kΩ 1/4W resistor**
- Ensures Vgs stays negative (pulled to GND)
- Prevents gate floating during transients
- Low power dissipation (~14mW @ 12V steady-state)
- RC time constant with gate capacitance ~100ns (fast switching)

---

## Body Diode Behavior

The AO3401A integrates a **body diode** (between Source and Drain, arrow pointing to Drain):

### Forward Direction (Correct Polarity, MOSFET ON)
- Body diode is reverse-biased (no current through diode)
- Current flows through low Rds(on) path (~0.14Ω)
- Voltage drop: **ΔV = I × Rds(on)** ≈ 4.2A × 0.14Ω = 0.59V

### Reverse Direction (Wrong Polarity, MOSFET OFF)
- Body diode is **forward-biased** (conducts)
- Reverse current limited by diode forward voltage (~0.7V)
- **Critical:** The diode conducts in reverse polarity, potentially damaging the load!
- **Solution:** Add external **Schottky diode** in series with Drain for lower voltage drop

---

## Advanced Schematic with Schottky Bypass (Lower Drop)

```
    +12V_IN
       |
       +--------+
              [R1]
              10kΩ
               |
         +-----+----- Gate (G)
         |
        [M1]
       D |  S
         |  |
        [D1] +------- +12V_OUT
        BAT43 (Schottky, 0.25V drop @ 2A)
         |  |
        GND GND
```

### Schottky Diode Selection

| Part | Forward Voltage | Max Current | Notes |
|---|---|---|---|
| **BAT43** | ~0.25V @ 2A | 0.5A | Ultra-low drop, small SOD-123 |
| **1N5818** | ~0.35V @ 2A | 1A | Common, low cost |
| **SB140** | ~0.45V @ 1A | 1A | Through-hole option |
| **STPS2L30** | ~0.45V @ 2A | 2A | SMD, better for higher current |

**Note:** Schottky diode adds ~0.3-0.4V reverse voltage drop to protect load. Choose based on current budget.

---

## Thermal Calculations

### Steady-State Power Dissipation (MOSFET ON)

Given:
- Vgs = -10V (Gate pulled to GND, 10V below Source)
- Rds(on) = 0.14Ω (at Vgs = -4.5V; approximate for Vgs = -10V)
- Load current: I = 2A

**P_dissipated = I² × Rds(on) = (2A)² × 0.14Ω = 0.56W**

**Junction temperature:**
Tj = Ta + (P × θja)
- θja (junction-to-ambient) = 125°C/W (AO3401A in SOT-23)
- Ta (ambient) = 25°C
- Tj = 25°C + (0.56W × 125°C/W) ≈ **95°C** ✓ Safe

### Higher Current Example (I = 4A)

**P = (4A)² × 0.14Ω = 2.24W**
**Tj = 25°C + (2.24W × 125°C/W) ≈ 305°C** ✗ Exceeds max 150°C

**Solution for 4A:** Add heatsink or choose MOSFET with lower Rds(on).

---

## Alternative P-Channel MOSFETs for 12V

### Direct Replacements (Pin-Compatible, SOT-23)

| Part Number | Rds(on) @ Vgs=-10V | Vds(max) | Id(max) | Cost | Notes |
|---|---|---|---|---|---|
| **AO3401A** | 0.14Ω (typical) | 20V | 4.2A | $$ | Recommended, balanced performance |
| **AO3406A** | 0.016Ω | 30V | 12A | $$$ | Lower resistance, overkill for low-current apps |
| **BSS84** | 0.9Ω | 20V | 0.13A | $ | Low current only, not suitable |
| **PMV3310** | 0.15Ω | 20V | 3.7A | $$ | Nearly identical to AO3401A |

### Higher Current (SOT-223 / SOIC-8)

| Part Number | Rds(on) | Vds(max) | Id(max) | Package | Notes |
|---|---|---|---|---|---|
| **SI2319** | 0.12Ω | 20V | 3.5A | SOT-223 | Larger package, better heat dissipation |
| **AO3409A** | 0.018Ω | 30V | 13A | SOT-23 | High performance, cost-effective |
| **FDV301** | 0.25Ω | 20V | 0.5A | SOT-23 | Low current, cost-optimized |
| **SUP71040** | 0.003Ω | 40V | 30A | SO8 | Industrial 12V systems, overkill for most |

### Recommended Selection

| Load Current | Part | Rds(on) | Package | Reason |
|---|---|---|---|---|
| **< 1A** | AO3401A | 0.14Ω | SOT-23 | Minimal dissipation |
| **1-4A** | **AO3401A** | 0.14Ω | SOT-23 | **Best choice (small, cheap, efficient)** |
| **4-10A** | SI2319 | 0.12Ω | SOT-223 | Better thermal path, lower drop |
| **> 10A** | SUP71040 | 0.003Ω | SO8 | High current capability |

---

## Complete Bill of Materials (BOM)

### Standard Configuration (Recommended for 2A load)

| Qty | Reference | Part Number | Value | Package | Notes |
|-----|---|---|---|---|---|
| 1 | M1 | AO3401A | - | SOT-23 | P-channel MOSFET |
| 1 | R1 | RES-FILM-1/4W | 10kΩ | 0805 / 1/4W | Gate pull-down resistor |
| 1 | C1 (optional) | CAP-CERAMIC | 100nF | 0603 | Gate-Source bypass (EMI suppression) |

**Optional upgrades:**
- Add **BAT43** Schottky diode in series (D1) to reduce reverse voltage drop
- Add **100nF ceramic cap** between Gate and GND for EMI suppression

---

## PCB Layout Considerations

1. **Gate Trace:** Keep Gate trace short (< 2 inches) to minimize EMI pickup
2. **Ground Plane:** Use continuous ground plane under MOSFET for thermal dissipation
3. **Gate Resistor:** Place close to Gate pin (< 1mm)
4. **Bypass Capacitor (if used):** Place between Gate and GND, close to MOSFET
5. **Thermal Via:** If on 4+ layer board, add thermal vias under MOSFET drain pad

---

## Typical Application Schematic (Full Protection Circuit)

```
    +12V_IN ─────+
                 │
               [Fuse]  (5A, slow-blow)
                 │
                 +─────+
                 │    [R1]
                [M1]  10kΩ Gate
              AO3401A  │
                D │ S  │
                  │ │  G
                 [D1]──┴─── GND
                Schottky
              (optional)
                  │ │
                  └─┴────+12V_OUT
                         │
                        [Load]
                    (e.g., MCU,
                     sensor, etc.)
                         │
                        GND
```

---

## Testing & Verification

### Test 1: Forward Polarity (Correct Insertion)
1. Apply +12V to input, GND to ground
2. Measure output voltage: Should read **~11.3-11.9V** (depends on load and Rds(on) drop)
3. Measure Gate voltage: Should read **0V** (pulled to GND)

### Test 2: Reverse Polarity (Wrong Insertion)
1. Apply GND to +12V terminal, +12V to GND terminal
2. Measure output voltage: Should read **0V** (or < 0.3V if Schottky diode is present)
3. Measure Gate voltage: Should still read **0V** (pulled to GND, always safe)
4. **Verify downstream circuitry is NOT damaged**

### Test 3: Transient Protection
1. Hot-swap input (connect/disconnect while powered)
2. Observe no voltage spikes on output (oscilloscope, 1-5V range)
3. Verify load remains functional after multiple insertions

---

## Design Rules Summary

| Rule | Value | Reason |
|---|---|---|
| Gate pull-down resistor | 10kΩ (typical) | Ensures Vgs stays negative when Gate floating |
| Max MOSFET Vds | 20V (AO3401A) | 12V nominal + transient margin |
| Recommended fuse | 5A slow-blow | Protects input circuit from shorts |
| Bypass capacitor (Gate) | 100nF ceramic | EMI suppression (optional but recommended) |
| Schottky diode | BAT43 (optional) | Reduces reverse voltage drop for sensitive loads |
| Gate-Source voltage | -10V to -12V (ON) | Ensures full MOSFET conduction |

---

## Troubleshooting

| Symptom | Cause | Solution |
|---|---|---|
| Load doesn't turn on in forward polarity | Vgs not negative enough | Check Gate pull-down resistor connection |
| Load turns on in reverse polarity | MOSFET body diode conducting | Add external Schottky diode in series |
| High voltage drop (~2V) in forward polarity | Rds(on) too high or undersized MOSFET | Upgrade to lower Rds(on) part (e.g., SI2319) |
| Gate voltage fluctuates | EMI pickup on gate trace | Add 100nF bypass capacitor, shorten gate traces |
| MOSFET gets hot (> 80°C) | Excessive current or inadequate dissipation | Add heatsink or upgrade package size |

---

## References

- **AO3401A Datasheet:** Alpha & Omega Semiconductor
- **Body Diode Conduction:** Reverse recovery at -12V input may cause brief current spike
- **Gate Charge:** ~15nC (AO3401A), negligible for DC-only applications

---

*Last Updated: 2026-04-05*
*Application: 12V Battery/Automotive Reverse Polarity Protection*
