yunusdanabas/evka_position/firmware/src/CmdTcpServer.h

#ifndef CMD_TCP_SERVER_H
#define CMD_TCP_SERVER_H

#include "SphericalSensor.h"

#if ENABLE_WIFI && ENABLE_CMD_TCP

#include <WiFi.h>

class CmdTcpServer {
public:
    CmdTcpServer();
    void begin();
    void poll();                    // Call from loop() — accept clients, read commands
    void broadcastPosition(float x, float y, float z);
    void broadcastSensorData(float r, float theta, float phi,
                             uint8_t valid, uint32_t frame);
    void sendToAllClients(const char* msg);
    String takePendingCommand();
    uint8_t clientCount();

private:
    static const uint8_t MAX_CLIENTS = 3;
    static const uint8_t CMD_RX_BUF_MAX = 128;  // Per-client rx buffer overflow guard
    WiFiServer _server;
    WiFiClient _clients[MAX_CLIENTS];
    String     _rxBuffers[MAX_CLIENTS];
    bool       _rxOverflow[MAX_CLIENTS];
    static const uint8_t CMD_QUEUE_SIZE = 4;
    static const size_t  CMD_MAX_LEN    = 128;
    char    _cmdQueue[CMD_QUEUE_SIZE][CMD_MAX_LEN + 1];
    uint8_t _cmdHead  = 0;
    uint8_t _cmdTail  = 0;
    uint8_t _cmdCount = 0;

    bool enqueueCommand(const String& line);
    void handleLine(uint8_t clientIdx, const String& line);
};

#endif // ENABLE_WIFI && ENABLE_CMD_TCP
#endif // CMD_TCP_SERVER_H
